NT7S/Yamhill/PCB/YamhillFrontPanel/YamhillFrontPanelFront.png

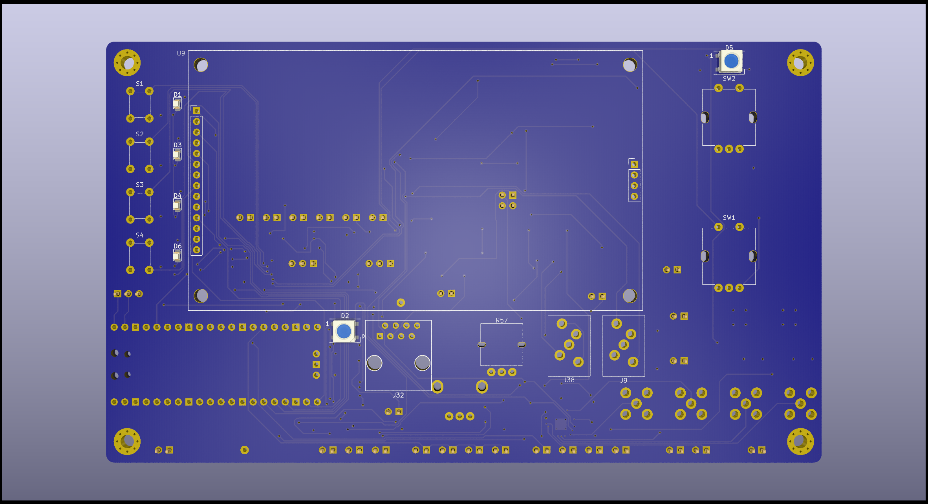
PCB/YamhillFrontPanel/YamhillFrontPanelFront.png
