NT7S/Yamhill/SPICE/AFAmp.asc

C1: cap; 10µ
C2: cap; 10µ
C3: cap; 10µ
C4: cap; 1µ
C5: cap; 10µ
C7: cap; 1µ
M2: nmos; 2N7002
M3: nmos; 2N7002
R1: res; 100k
R2: res; 100k
R3: res; 10k
R4: res; 10k
R5: res; 100
R6: res; 1k
R7: res; 100k
R10: res; 1k
R11: res; 10k
R12: res; 100k
R14: res; 470
R15: res; 1k
U1: UniversalOpAmp2; Avol=1Meg GBW=22Meg Slew=17Meg
U2: UniversalOpAmp2; Avol=1Meg GBW=22Meg Slew=17Meg
V1: voltage; 5
V2: voltage; PULSE(0 5 0 1m 1m 10m 20m); Rser=10
V3: voltage; SINE(0 2m 1k)
Named nets: 0, +V, OUT, IS, IN, VG, KEY
.tran 200m
